asablue65/iMac-5k-monitor-conversion/PNG/IMG_7835.png

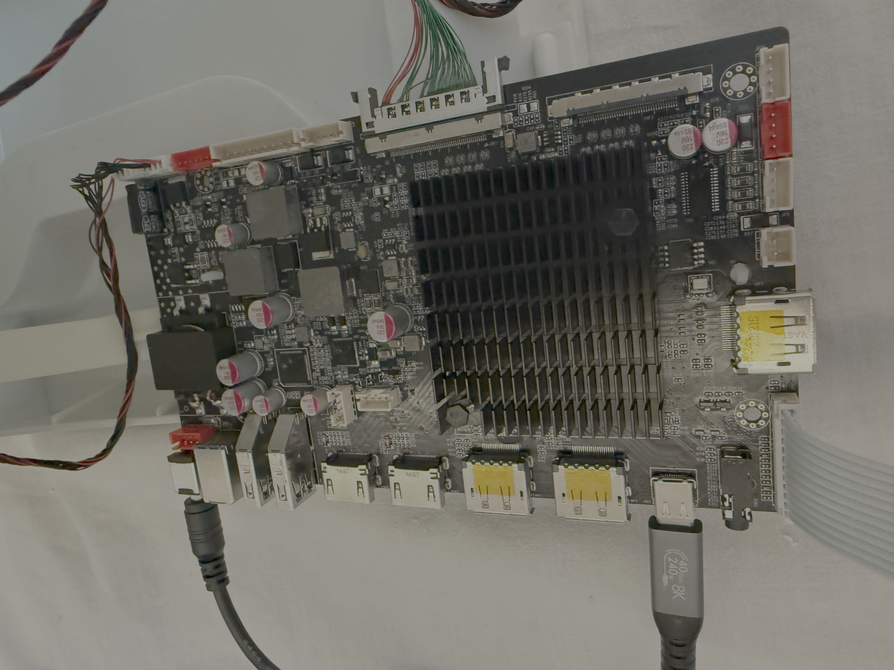
PNG/IMG_7835.png
