asablue65/iMac-5k-monitor-conversion/PNG/IMG_7916.png

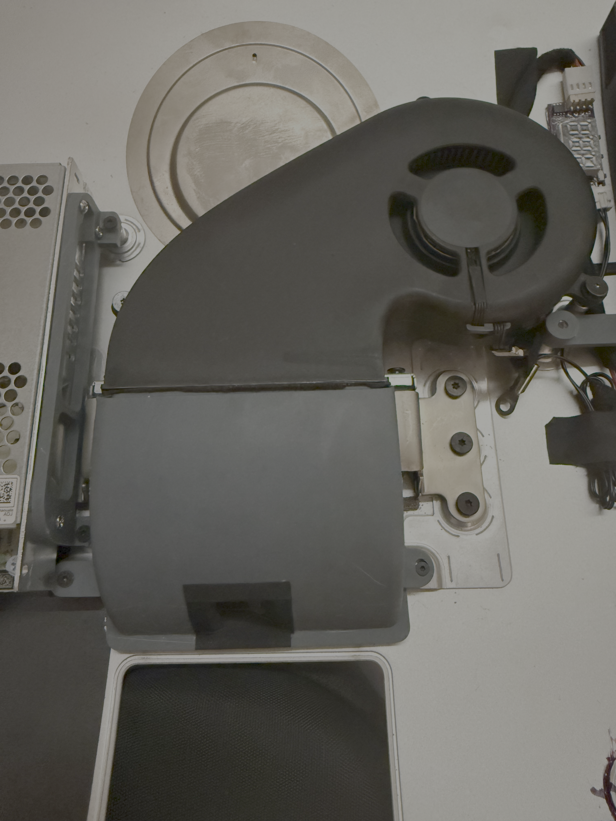
PNG/IMG_7916.png
