asablue65/iMac-5k-monitor-conversion/PNG/IMG_7940.png

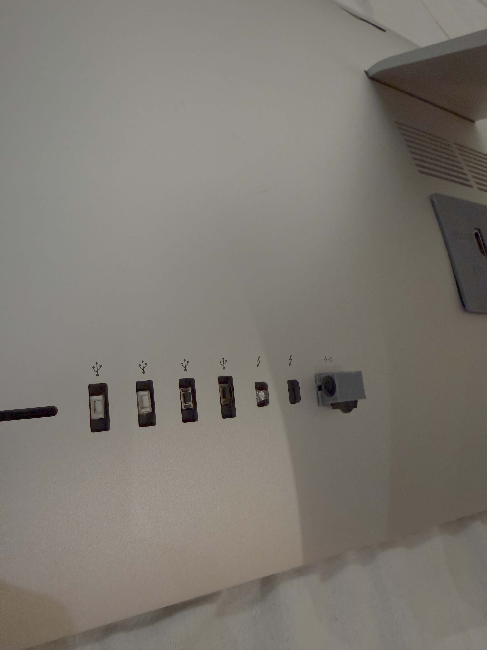
PNG/IMG_7940.png
