asablue65/iMac-5k-monitor-conversion/PNG/M3-5-5.png

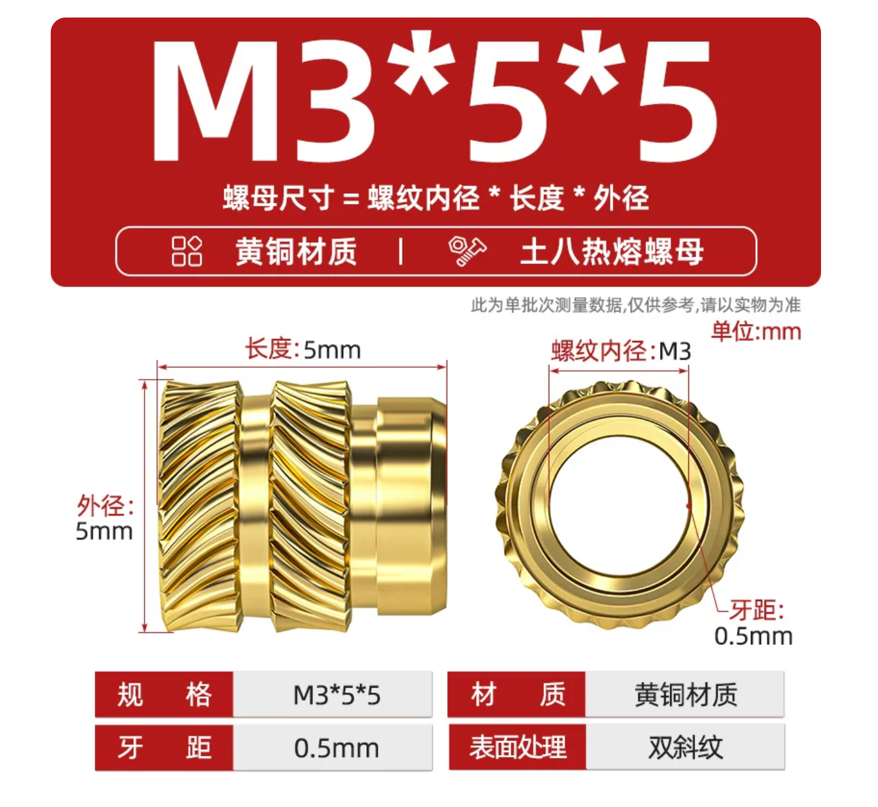
PNG/M3-5-5.png
