asablue65/iMac-5k-monitor-conversion/PNG/M4-5-5.png

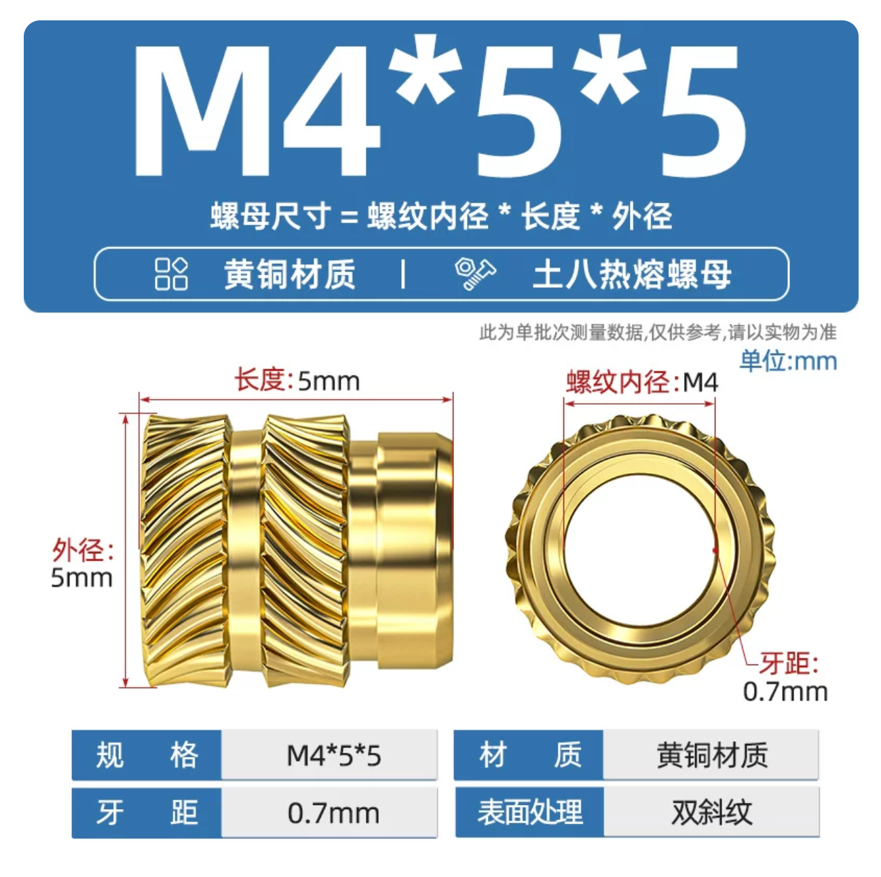
PNG/M4-5-5.png
