asablue65/iMac-5k-monitor-conversion/PNG/M16-2-250V.png

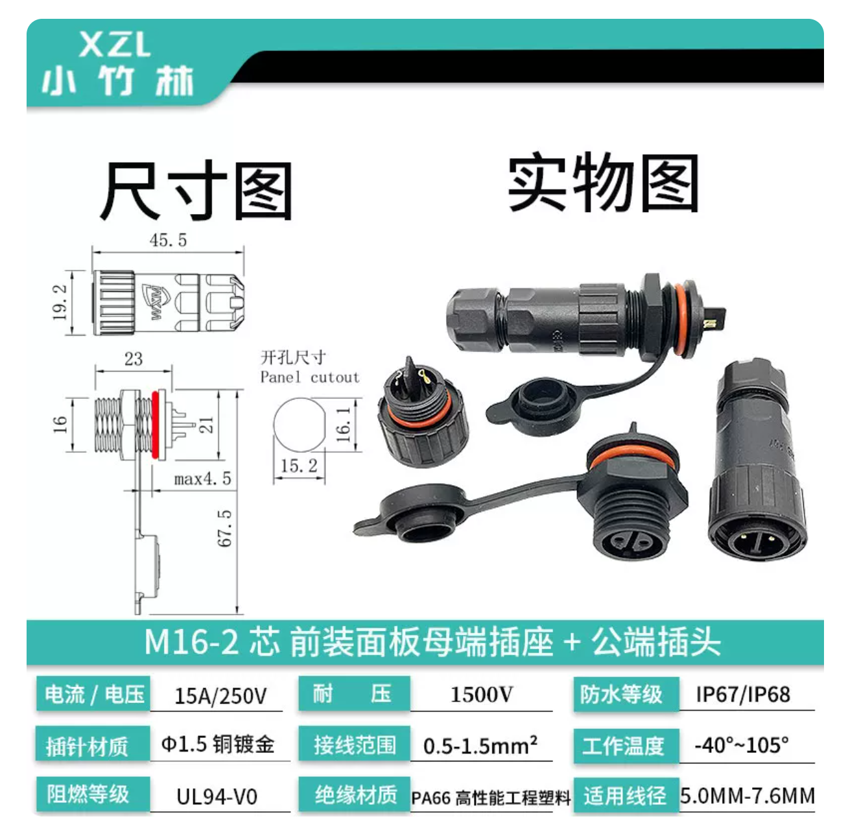
PNG/M16-2-250V.png
