asablue65/iMac-5k-monitor-conversion/PNG/R1820.jpeg

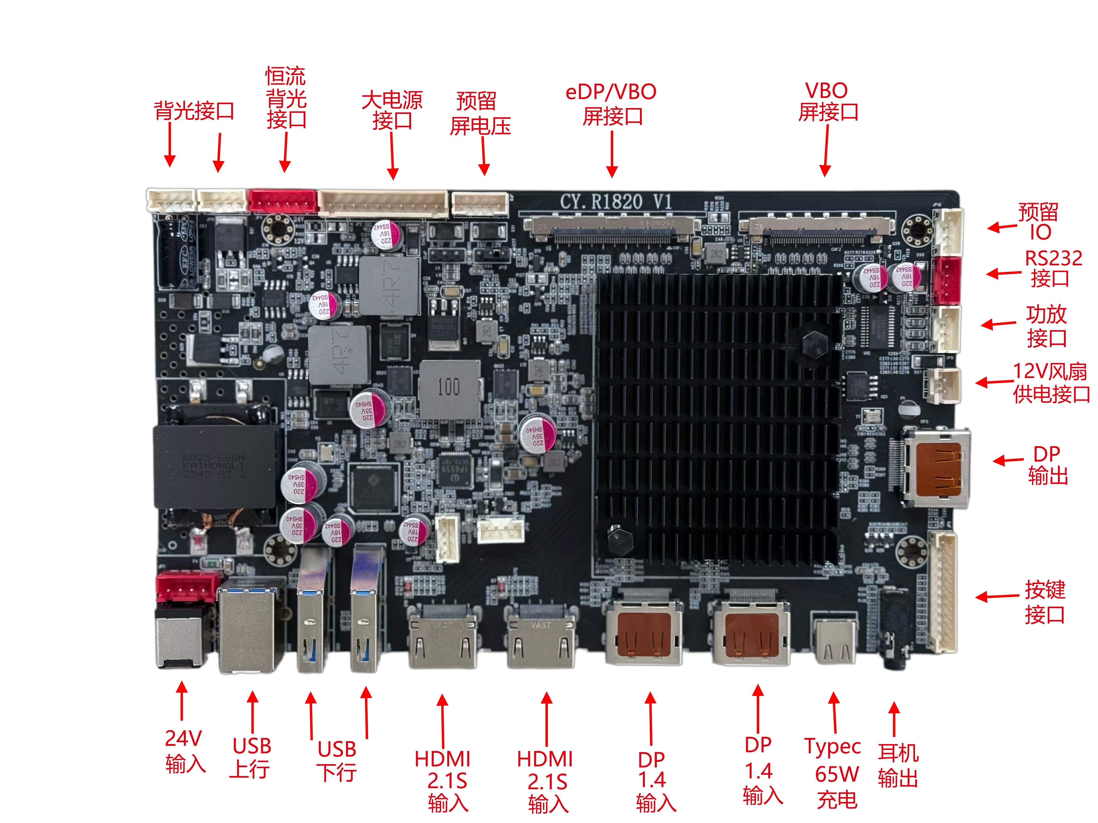
PNG/R1820.jpeg
